jpfutalef/Current-Measurement-Board/boards/pcb/Pictures/IMG_6334.JPG

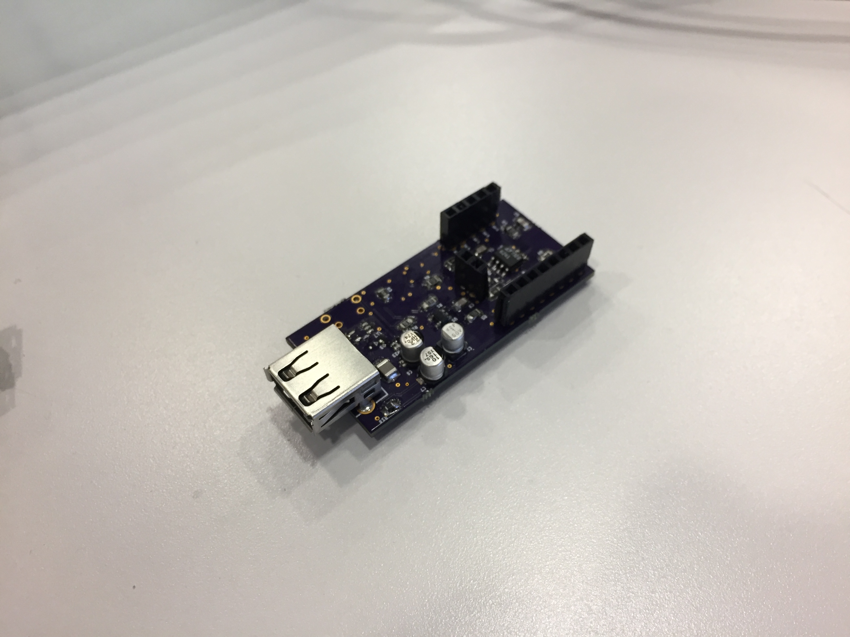
boards/pcb/Pictures/IMG_6334.JPG
