jpfutalef/Current-Measurement-Board/boards/pcb/Pictures/IMG_6335.JPG

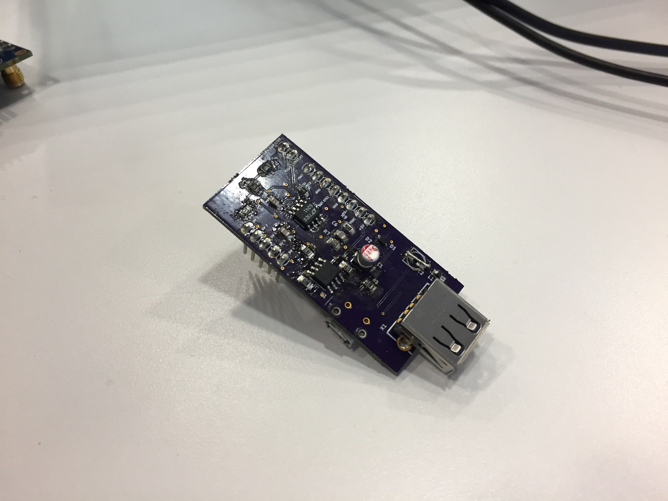
boards/pcb/Pictures/IMG_6335.JPG
