jpfutalef/Current-Measurement-Board/boards/pcb/Pictures/IMG_6336.JPG

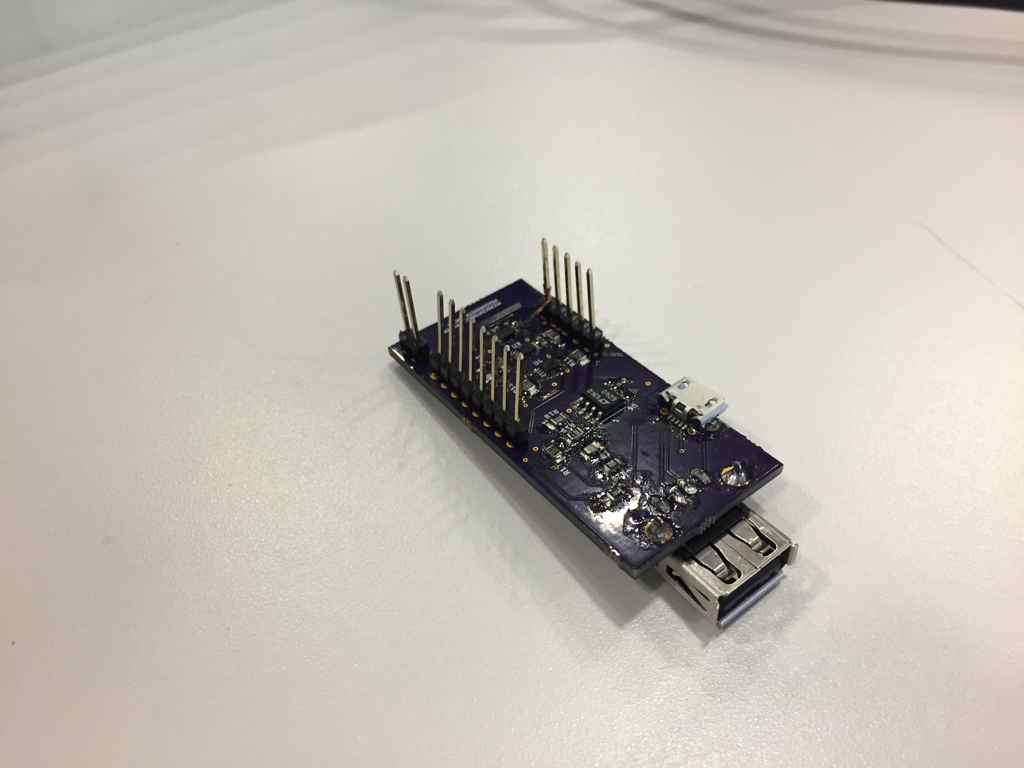
boards/pcb/Pictures/IMG_6336.JPG
