jpfutalef/Current-Measurement-Board/boards/pcb/Pictures/IMG_6337.JPG

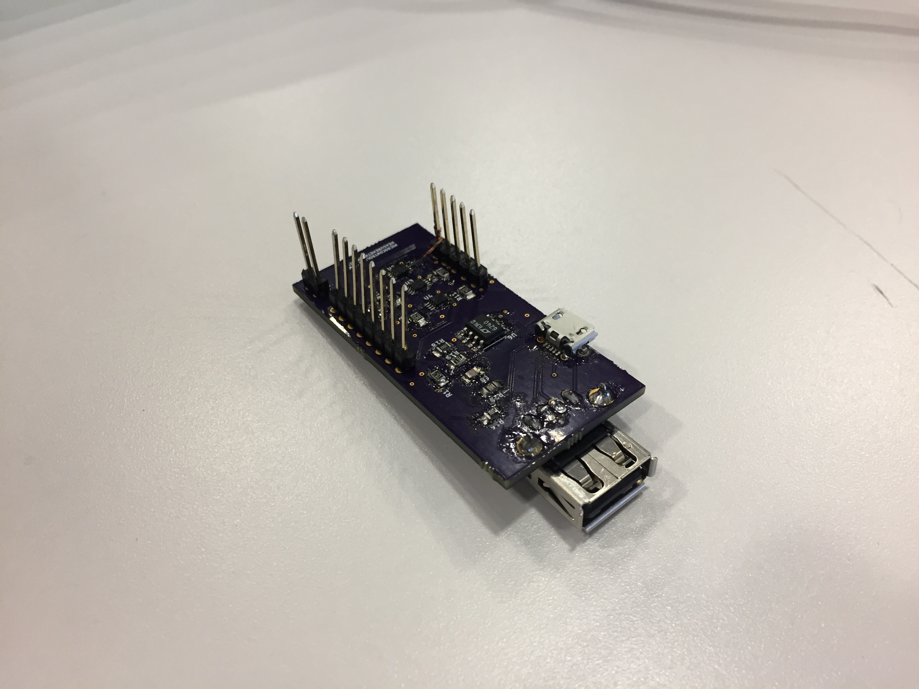
boards/pcb/Pictures/IMG_6337.JPG
