jpfutalef/Current-Measurement-Board/boards/pcb/Pictures/IMG_6338.JPG

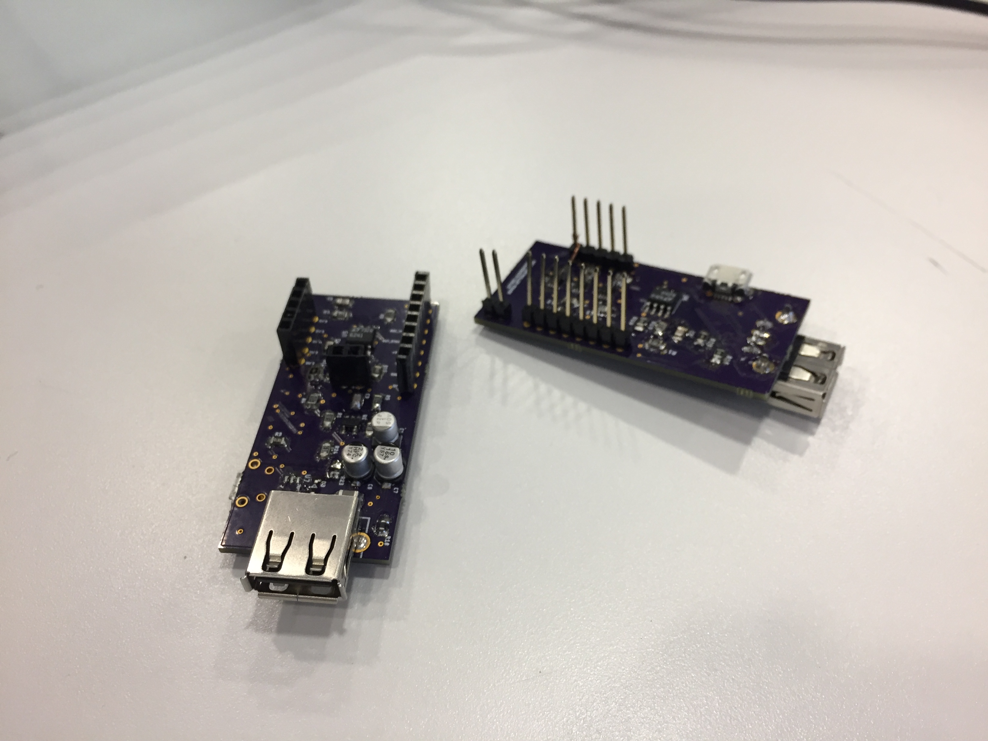
boards/pcb/Pictures/IMG_6338.JPG
