jpfutalef/Current-Measurement-Board/boards/pcb/Pictures/IMG_6339.JPG

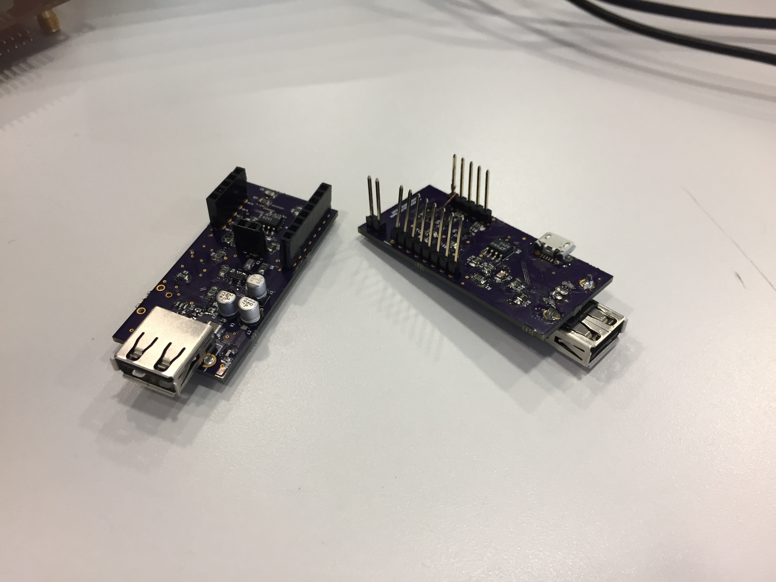
boards/pcb/Pictures/IMG_6339.JPG
