jpfutalef/Current-Measurement-Board/ltspice/v1_lmp2011_lt624X.asc

C3: cap; .1µ
C4: cap; 10p
C5: cap; 10p
C6: cap; 10p
C7: cap; 10p
C8: cap; 1µ
C9: cap; 15p
C10: cap; 1µ
IMCU: current; PULSE(0 50m 0 2u 2u 50u 100u 1000)
L1: ind; 10µ
R1: res; 1k
R2: res; 10K
R3: res; 4.7; tol=.1 pwr=100m
R4: res; 100K
R5: res; 1Meg
R6: res; 10k
R7: res; 10k
R8: res; 100k
R9: res; 100k
R10: res; 60.4k
R11: res; 10k
R14: res; 10k; tol=.1
R15: res; 187k; tol=.1
R16: res; 100k; tol=.1
R21: res; 51k; tol=.1
R22: res; 20k
R23: res; 10k
R24: res; 20k
R25: res; 10k
R26: res; .9; tol=1
R27: res; 49.9
R28: res; 49.9; tol=.1
R29: res; 1Meg
R30: res; 1Meg
R31: res; 49.9
U1: LMP2011
U2: LTC6241
U3: LT3461
U5: LTC6240
U6: LTC6241
V1: voltage; 5
V3: voltage; 5
Named nets: 0, Vcc, VBAT, VOUT1, 8V68, ADC__VOLT, ADC__LOWRANGE, ADC__HIGHRANGE
.tran 0 3m 0
x10 GAIN
Calibration Set
Target MCU (load)
Shunt Res
SW1
SW2
SW3
SW4
SW5
SW6
x.5 GAIN
x197 GAIN
x1.51 GAIN
(>60mA conectar 0.8R)
