jpfutalef/Current-Measurement-Board/ltspice/v1_ltc2055_lt624X.asc

C1: cap; 1µ
C2: cap; .1µ
C3: cap; .1µ
C4: cap; 15p
C5: cap; 1µ
C6: cap; 10p
C7: cap; 10p
C8: cap; 10p
C9: cap; 10p
IMCU: current; PULSE(0 65m 0 5u 5u 30u 60u 10000)
L1: ind; 10µ
R1: res; 1k; tol=.1
R2: res; 10K; tol=.1
R3: res; 5; tol=.1
R4: res; 100K; tol=.1
R5: res; 1Meg; tol=.1
R6: res; 10k; tol=.1
R7: res; 10k; tol=.1
R8: res; 100k; tol=.1
R9: res; 100k; tol=.1
R10: res; 10k; tol=.1
R11: res; 190k; tol=.1
R12: res; 100k; tol=.1
R13: res; 50k; tol=.1
R14: res; 20k
R15: res; 10k
R16: res; 20k
R19: res; 55
R21: res; 10k
R22: res; 45.5k
R23: res; 10k
R25: res; 55; tol=.1
R26: res; .8; tol=1
R27: res; 55
R28: res; 1Meg
R29: res; 1Meg
U1: LTC2055
U2: LTC6240
U3: LTC6241
U4: LTC6241
U5: LT3461
V1: voltage; 5
V3: voltage; 3
Named nets: 0, VBAT, VOUT1, 7V, Vcc, ADC__VOLT, ADC__LOWRANGE, ADC__HIGHRANGE
.tran 0 3m 2m .1u
x10 GAIN
x200 GAIN
x1.5 GAIN
(>60mA conectar 0.8R)
Calibration Set
Target MCU (load)
x.5 GAIN
Shunt Res
SW1
SW2
SW3
SW4
SW5
SW6
