jpfutalef/Current-Measurement-Board/ltspice/v3_max4239_lt624X.asc

C1: cap; .1µ
C2: cap; .1µ
C3: cap; .1µ
C4: cap; 10p
C5: cap; 10p
C6: cap; 10p
C7: cap; 10p
IMCU: current; 0
R1: res; 1k; tol=.1
R2: res; 10K; tol=.1 pwr=.05
R3: res; 1; tol=.01 pwr=100m
R4: res; 100K; tol=.1
R5: res; 1Meg; tol=.1
R6: res; 1k; tol=.1 pwr=.05
R7: res; 1k; tol=.1 pwr=.05
R8: res; 100k
R9: res; 100k
R10: res; .9
R11: res; .9
R12: res; .9
R13: res; .9
R14: res; 10k; tol=1 pwr=.05
R15: res; 187k; tol=.1
R16: res; 51k; tol=.1
R17: res; .9
R21: res; 100k; tol=.1
R22: res; 20k; tol=.1
R23: res; 10k; tol=.1 pwr=.05
R24: res; 20k; tol=.1
R25: res; 10k; tol=.1 pwr=.05
R26: res; .9; tol=1 pwr=180m
R27: res; 49.9; tol=1 pwr=.05
R28: res; 49.9; tol=1 pwr=.05
R29: res; 1Meg
R30: res; 1Meg
R31: res; 49.9; tol=1 pwr=.05
U1: MAX4239
U2: LTC6241
U5: LTC6240
U6: LTC6241
V1: voltage; 5
V3: voltage; 5
Named nets: 0, Vcc, VBAT, VOUT1, ADC__VOLT, ADC__LOWRANGE, ADC__HIGHRANGE
x100 GAIN
Calibration Set
(R1 minCurrent: 5mA eq. 25mW=1/4W)
Target MCU (load)
Shunt Res
SW1
SW2
SW3
SW4
SW5
SW6
x.5 GAIN
x197 GAIN
x1.51 GAIN
(>60mA conectar 0.8R)
.dc IMCU 0 10u 1u
Imax Rshunt1 = 650mA
